ok1hra/3D-print-WX-station/3d-print/stl-output/3.stl

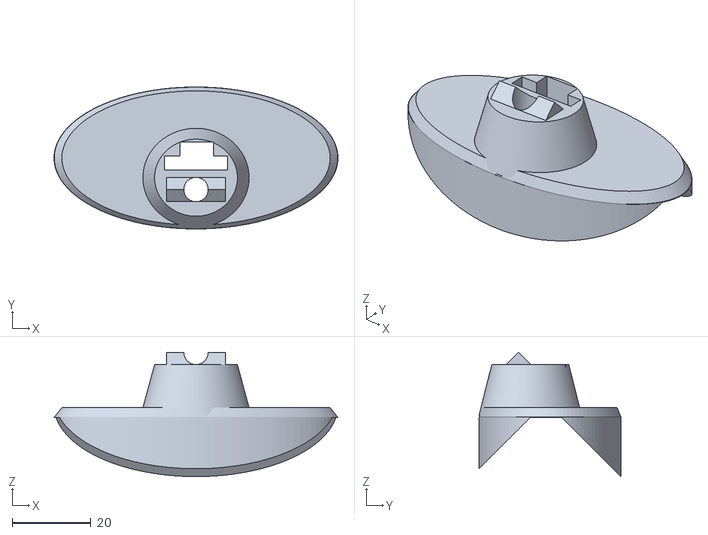
[picture p16: CAD file, 2023-08-25]
3d-print/stl-output/3.stl
72.0 x 36.0 x 31.5
