ok1hra/3D-print-WX-station/3d-print/stl-output/9.stl

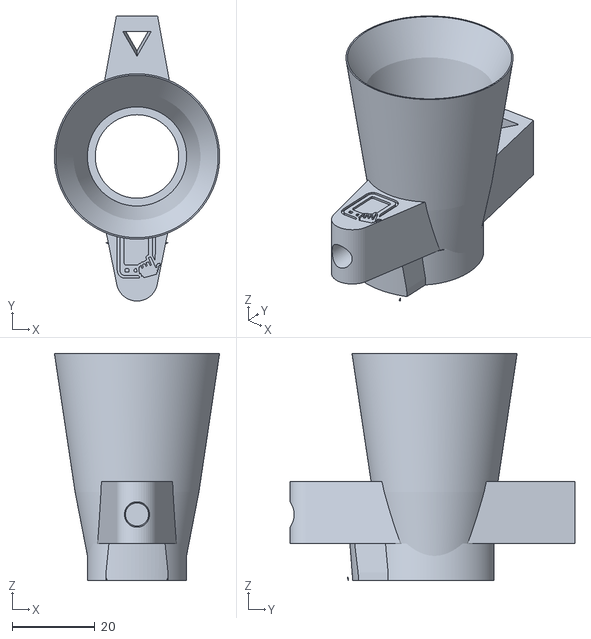
[picture p17: CAD file, 2023-08-25]
3d-print/stl-output/9.stl
40.0 x 69.0 x 55.0
