ok1hra/3D-print-WX-station/3d-print/stl-output/16.stl

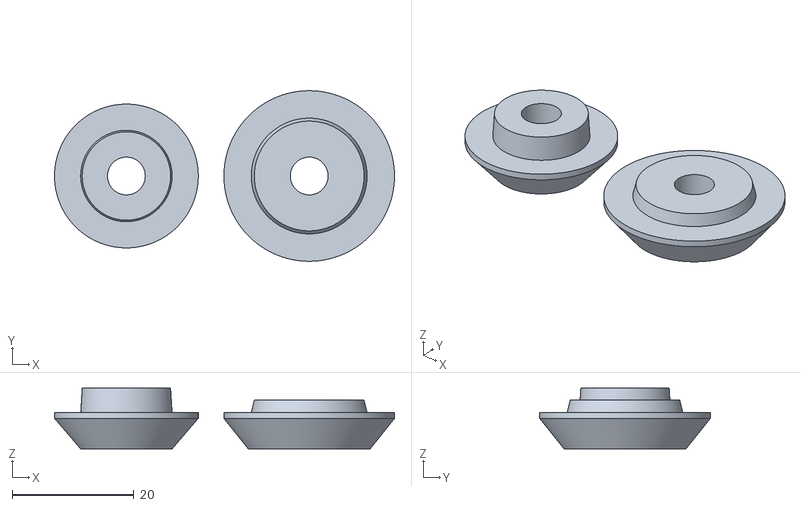
[picture p18: CAD file, 2023-08-25]
3d-print/stl-output/16.stl
55.8 x 28.0 x 10.0
