ok1hra/3D-print-WX-station/3d-print/stl-output/7.stl

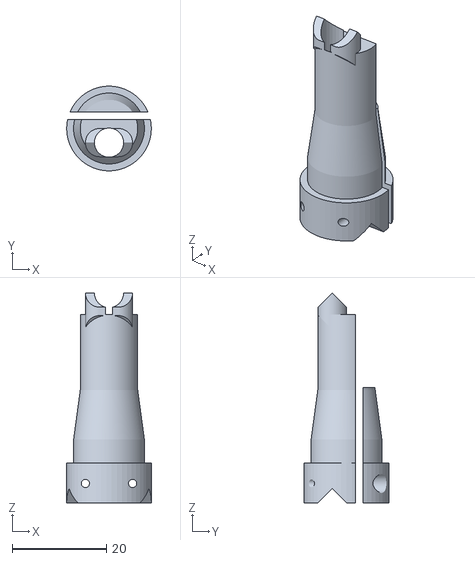
[picture p19: CAD file, 2023-08-25]
3d-print/stl-output/7.stl
18.0 x 18.0 x 44.6
