ok1hra/3D-print-WX-station/3d-print/stl-output/12.stl

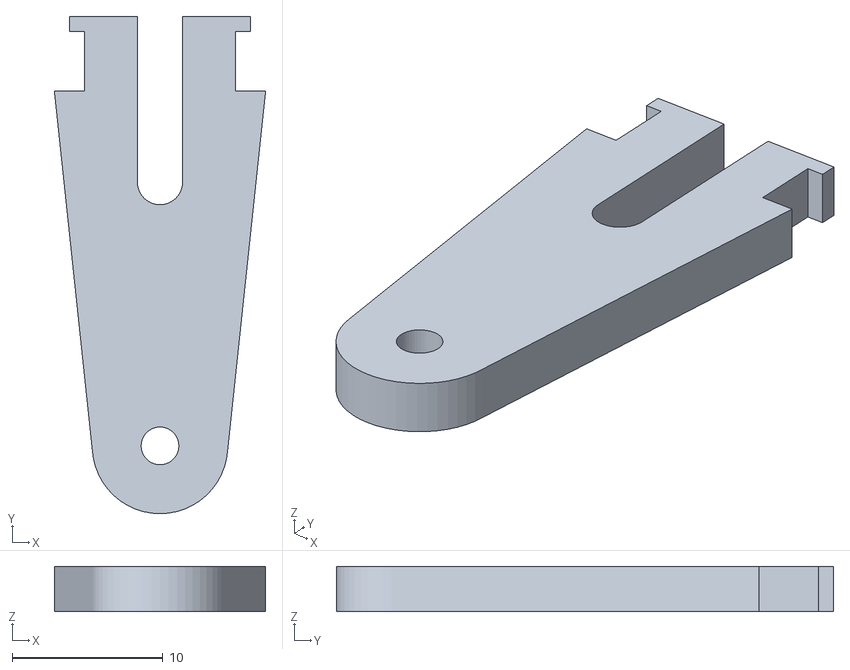
[picture p20: CAD file, 2023-08-25]
3d-print/stl-output/12.stl
14.0 x 33.0 x 3.00
