ok1hra/3D-print-WX-station/3d-print/stl-output/10.stl

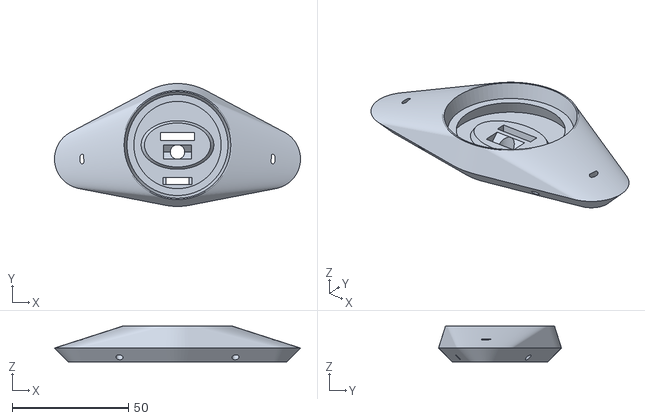
[picture p21: CAD file, 2023-08-25]
3d-print/stl-output/10.stl
106.0 x 53.0 x 15.5
