ok1hra/3D-print-WX-station/3d-print/stl-output/4.stl

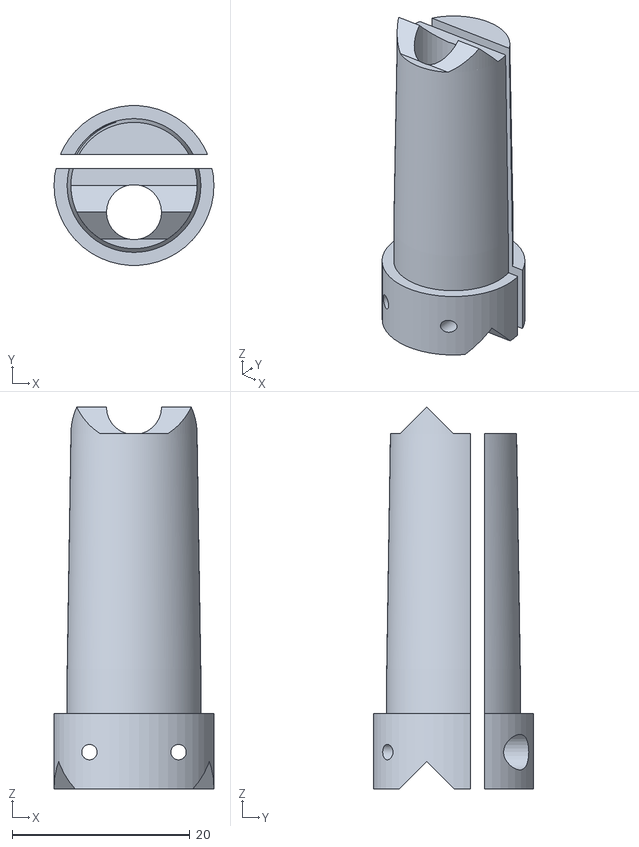
[picture p22: CAD file, 2023-08-25]
3d-print/stl-output/4.stl
18.0 x 18.0 x 43.0
