ok1hra/3D-print-WX-station/3d-print/stl-output/8.stl

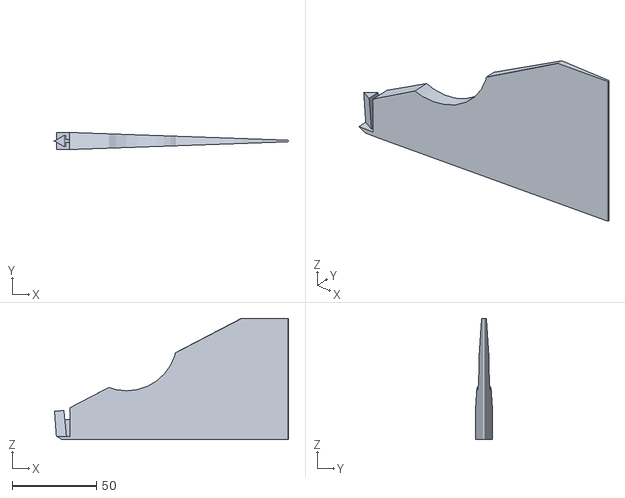
[picture p23: CAD file, 2023-08-25]
3d-print/stl-output/8.stl
138.7 x 10.0 x 72.0
