ok1hra/3D-print-WX-station/3d-print/stl-output/TRANSPARENT.3mf

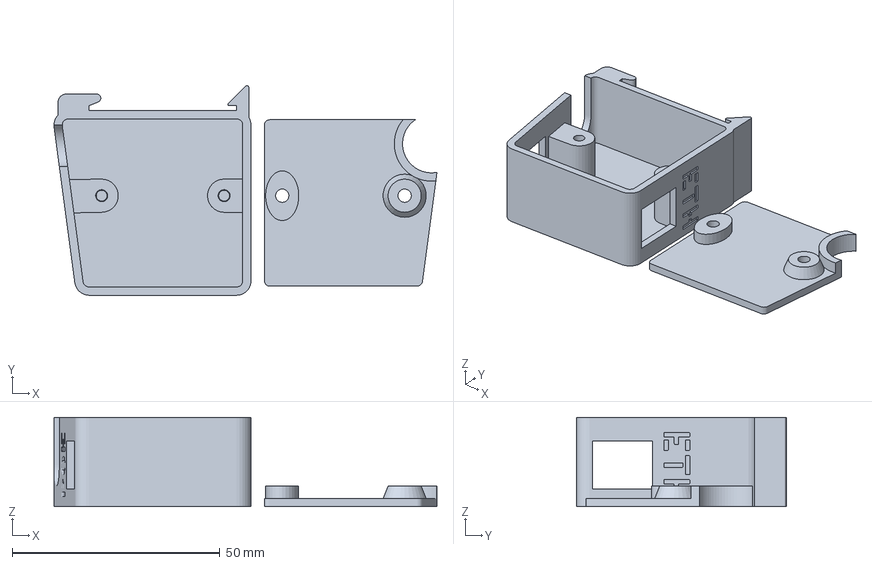
[picture p24: CAD file, 2023-08-25]
3d-print/stl-output/TRANSPARENT.3mf
92.3 x 50.5 x 21.5 mm
