ok1hra/3D-print-WX-station/3d-print/stl-output/13.stl

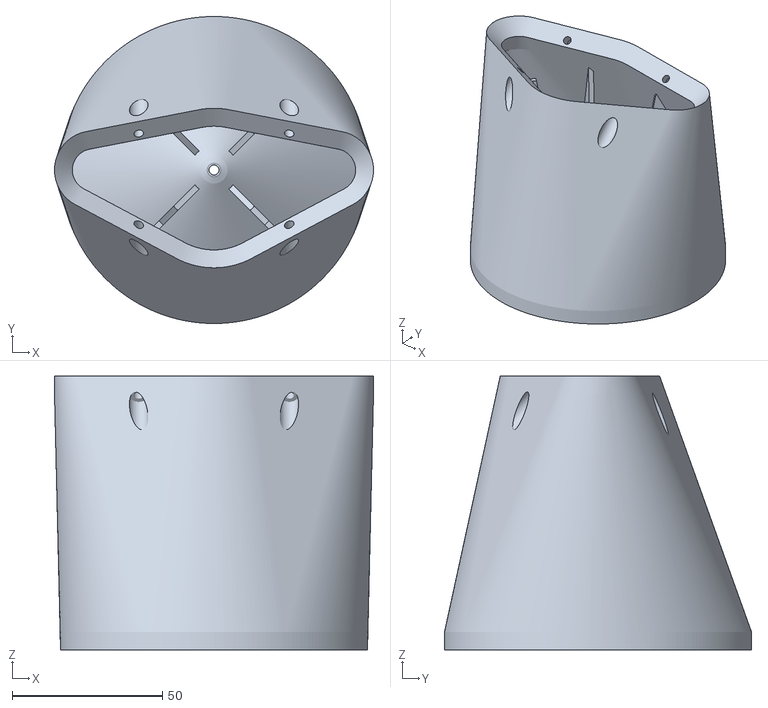
[picture p25: CAD file, 2023-08-25]
3d-print/stl-output/13.stl
106.0 x 102.0 x 90.9
